NathanWeiland10/AquaCleanPro/source/steering-system.hpp

#include "motor.hpp"
#define TURN_TIME 10

class SteeringSystem{
    public:
        SteeringSystem(Motor left, Motor right);

        void stop();

        void go();

        void turnRight();

        void turnLeft();

        void update();

        enum State{
            STOPPED,
            FORWARD,
            TURNING_LEFT,
            TURNING_RIGHT
        };

    private:
        Motor leftMotor;
        Motor rightMotor;
        int turnTimer;
        State state;
};
